kenhia/kTaskLight/images/IMG_1798.jpg

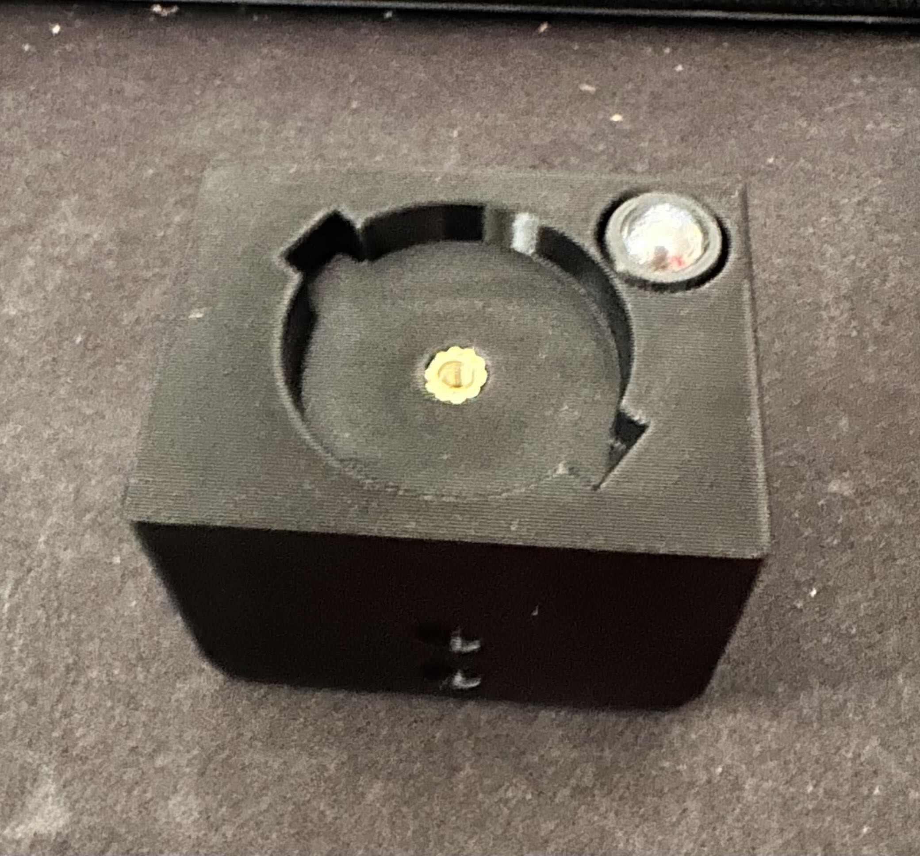
images/IMG_1798.jpg
