kenhia/kTaskLight/images/IMG_1799.jpg

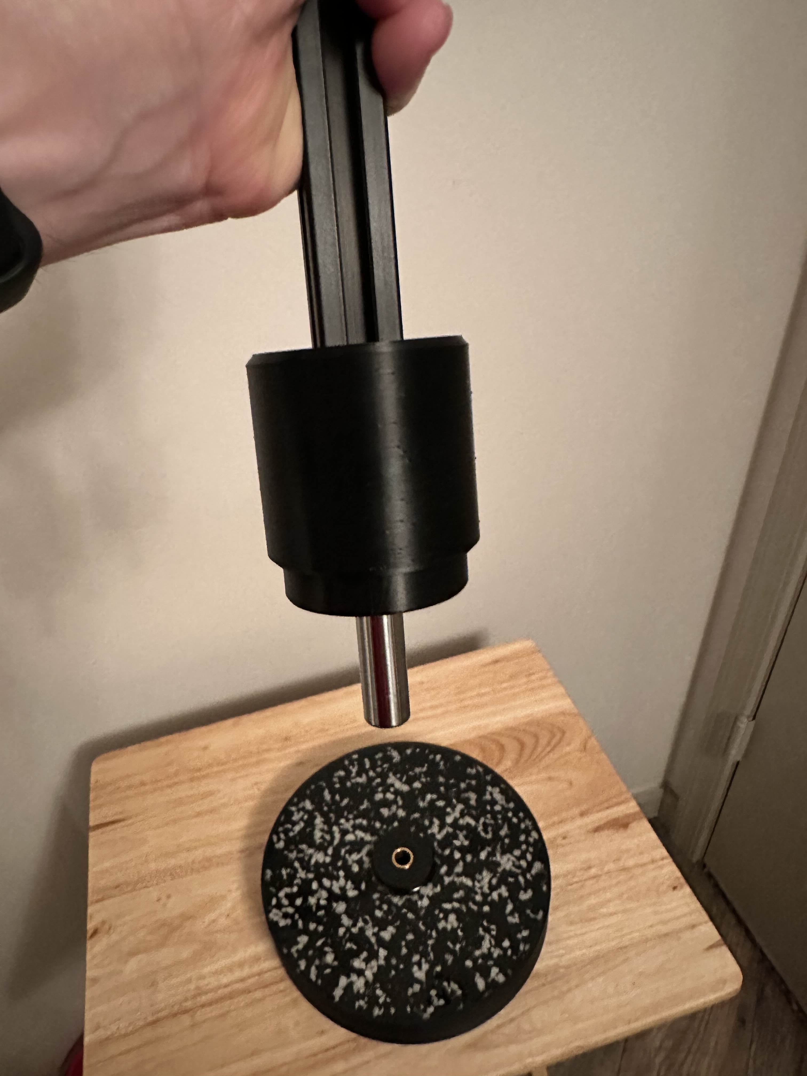
images/IMG_1799.jpg
