kenhia/kTaskLight/images/IMG_1803.jpg

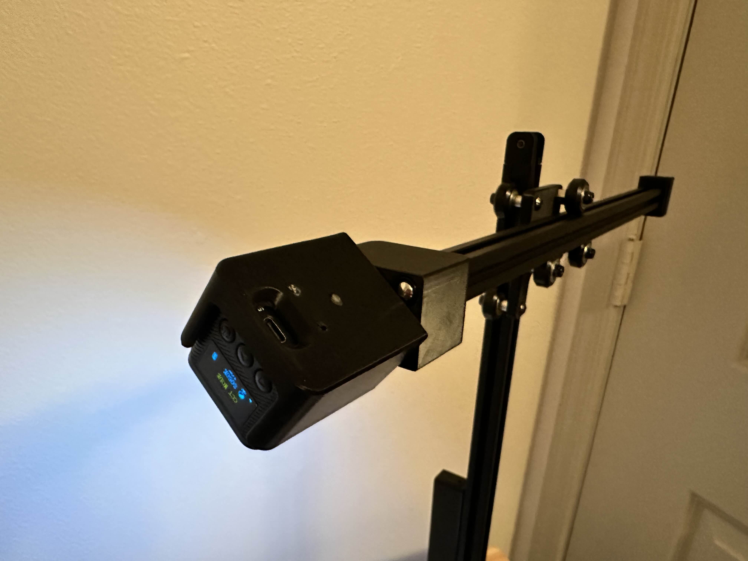
images/IMG_1803.jpg
