kenhia/kTaskLight/images/IMG_1804.jpg

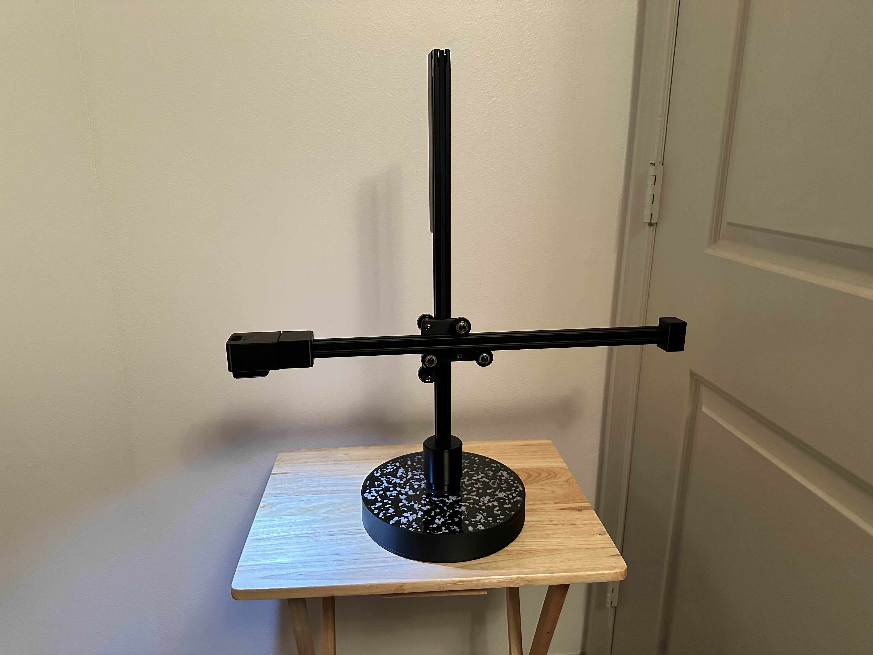
images/IMG_1804.jpg
