kenhia/kTaskLight/images/IMG_1805.jpg

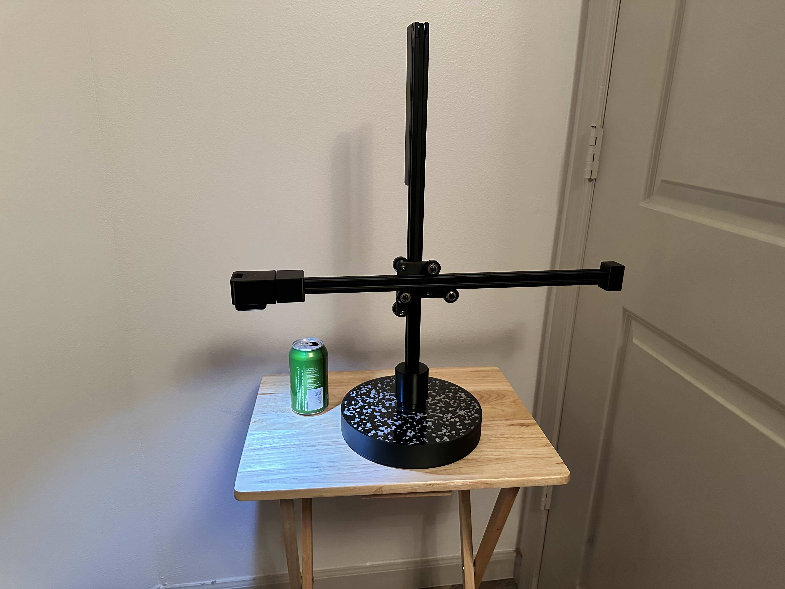
images/IMG_1805.jpg
