kenhia/kTaskLight/images/IMG_1806.jpg

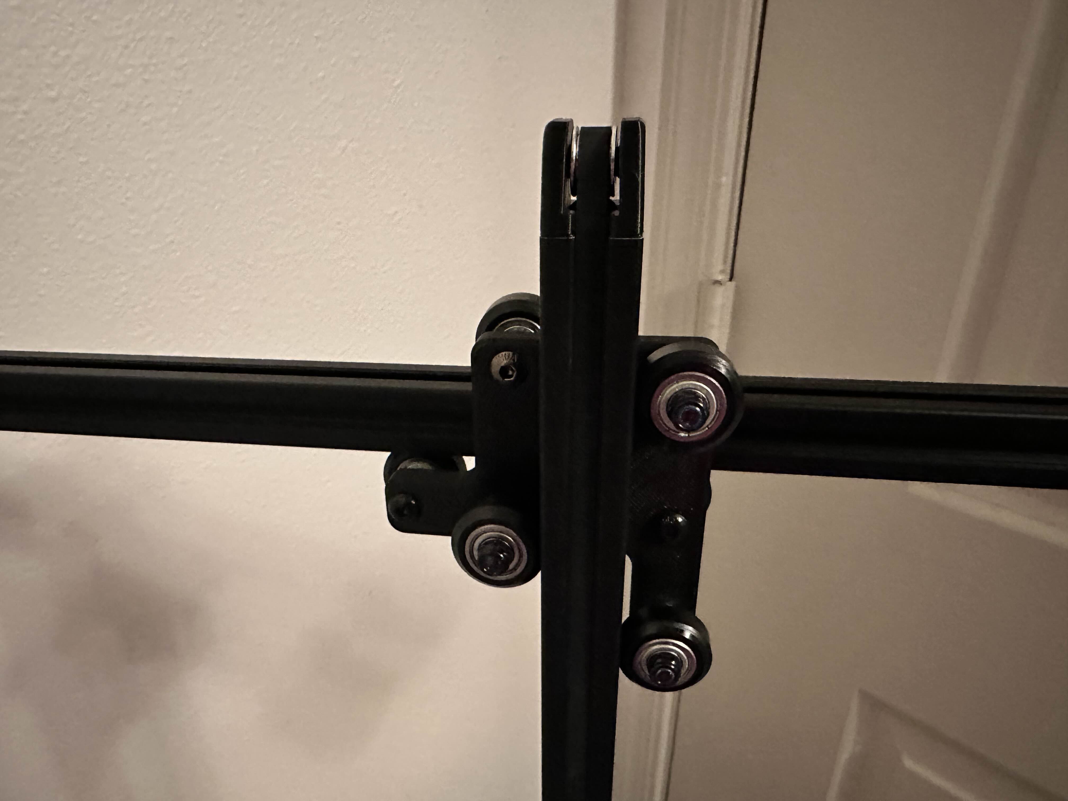
images/IMG_1806.jpg
