kenhia/kTaskLight/images/IMG_1807.jpg

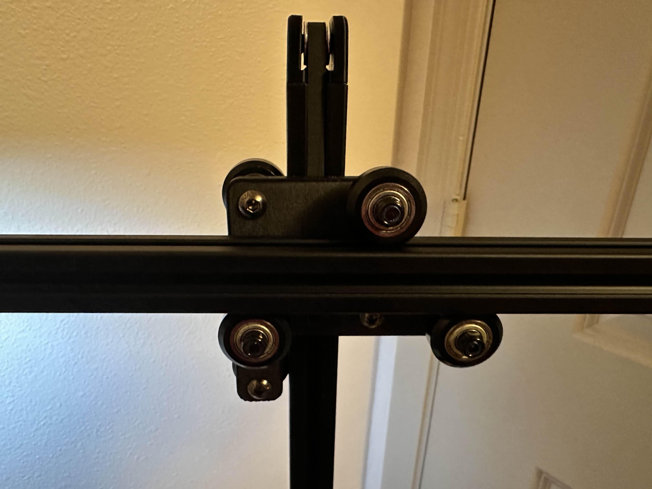
images/IMG_1807.jpg
