kenhia/kTaskLight/images/IMG_1808.jpg

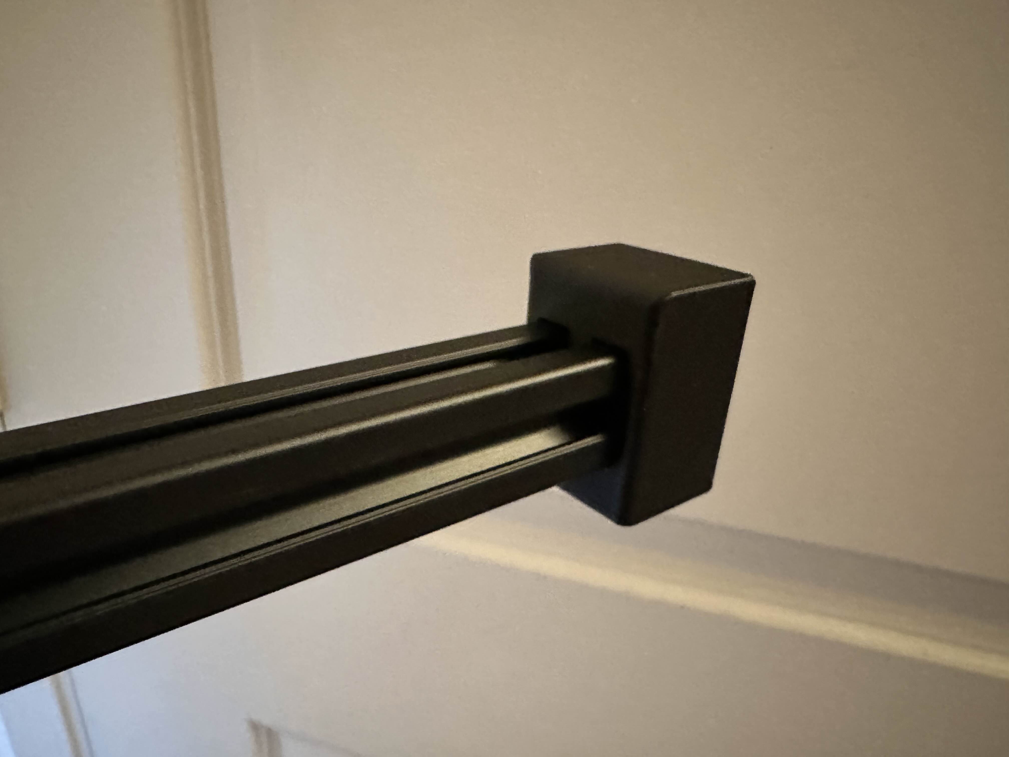
images/IMG_1808.jpg
