kenhia/kTaskLight/images/IMG_1809.jpg

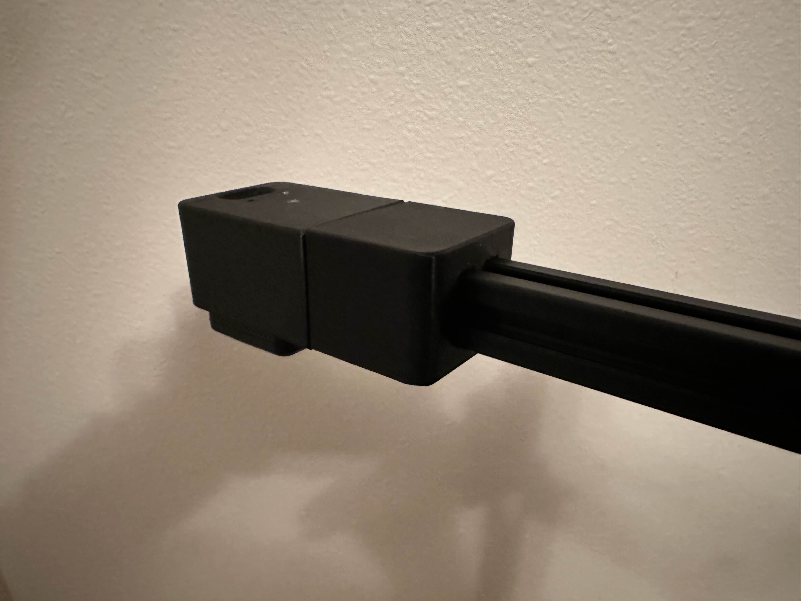
images/IMG_1809.jpg
