kenhia/kTaskLight/images/IMG_1811.jpg

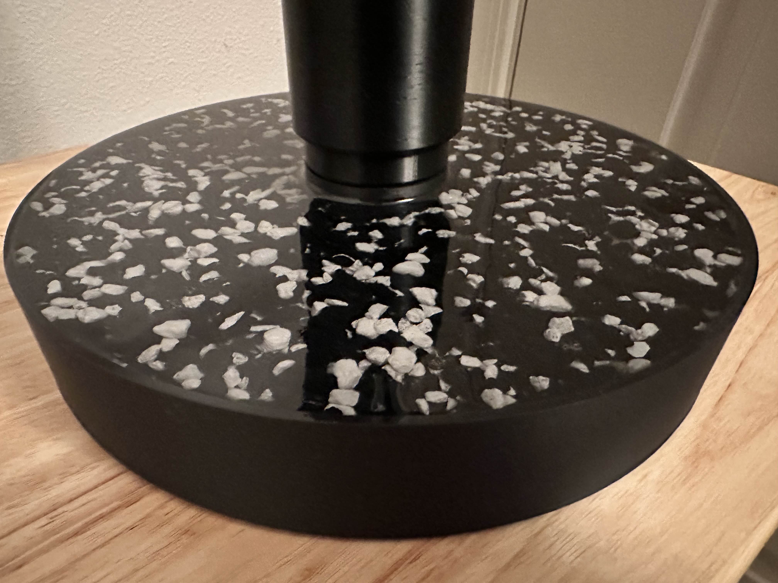
images/IMG_1811.jpg
